bpatters/wildlights/nrfworkspace/LEDProject/include/main.h

/* Copyright (c) 2012 Nordic Semiconductor. All Rights Reserved.
 *
 * The information contained herein is property of Nordic Semiconductor ASA.
 * Terms and conditions of usage are described in detail in NORDIC
 * SEMICONDUCTOR STANDARD SOFTWARE LICENSE AGREEMENT.
 *
 * Licensees are granted free, non-transferable use of the information. NO
 * WARRANTY of ANY KIND is provided. This heading must NOT be removed from
 * the file.
 *
 */

 /** @cond To make doxygen skip this file */
 
/** @file
 *
 * @defgroup ble_sdk_app_hrs_eval_main Main source file
 * @{
 * @ingroup ble_sdk_app_hrs_eval
 * @brief Main source file prototypes
 *
 */

#ifndef MAIN_H__
#define MAIN_H__

/**@brief External reference to the Battery Service. */
extern ble_bas_t                             bas;



#endif // MAIN_H__

/** @} */
/** @endcond */
